ngjstn/Alarm-Clock-Chaser/RPI_testing/image2.jpg

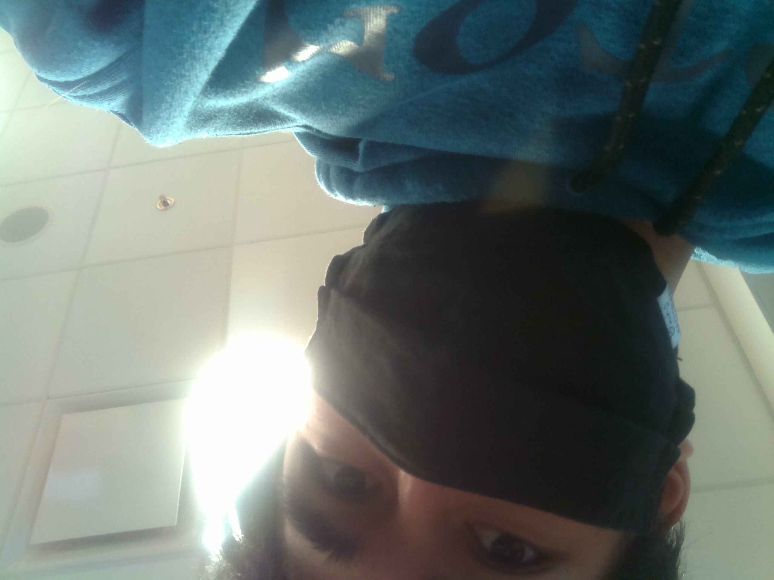
RPI_testing/image2.jpg
