ngjstn/Alarm-Clock-Chaser/RPI_testing/image3.jpg

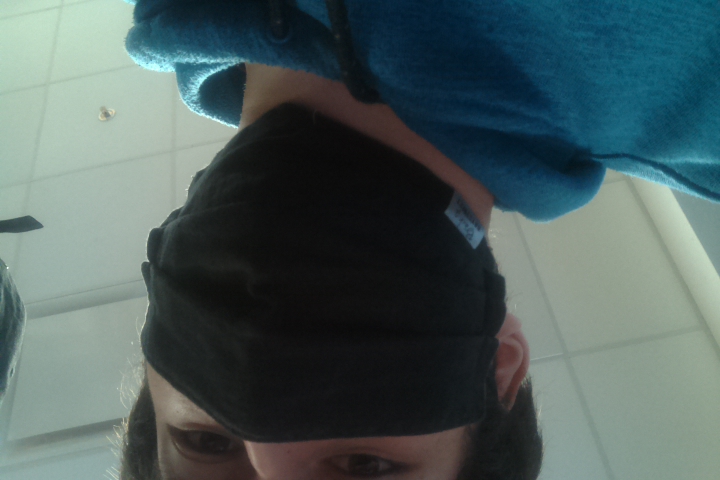
RPI_testing/image3.jpg
