ngjstn/Alarm-Clock-Chaser/RPI_testing/blinkatest.py

import time
import board
import digitalio

led = digitalio.DigitalInOut(board.D17)
led.direction = digitalio.Direction.OUTPUT

while True:
    led.value = True
    time.sleep(0.1)
    led.value = False
    time.sleep(0.1)
